ing-guillermo-quintero/Infra-Logistica/CADs/CAD_INFRA_LOG.jpeg

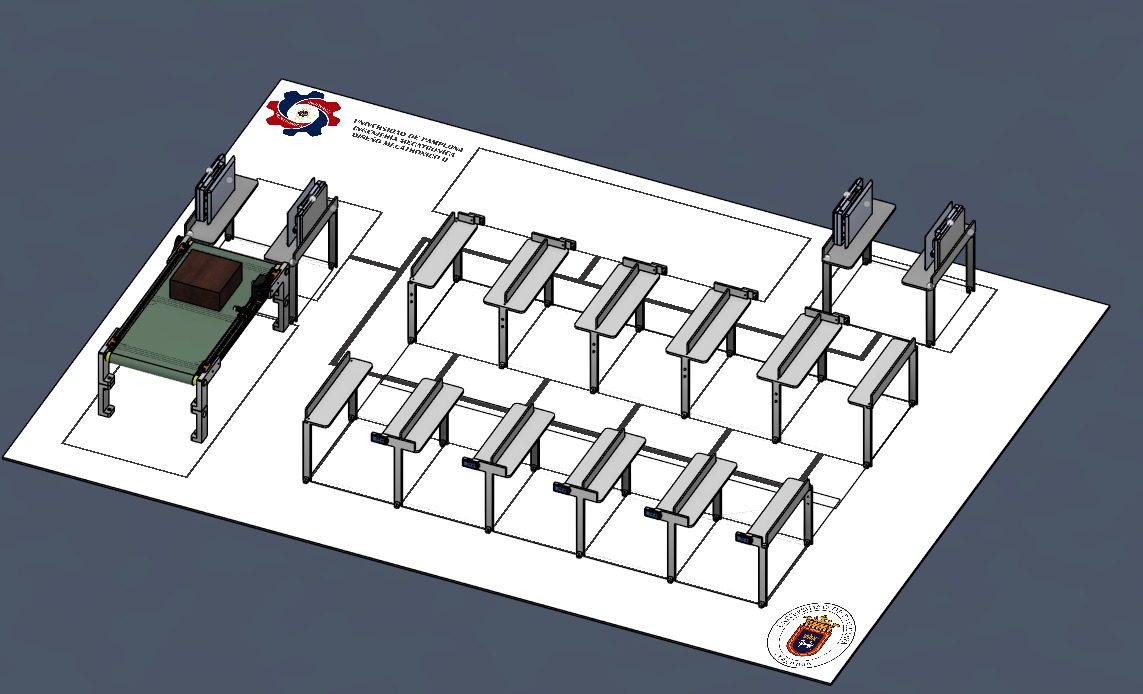
CADs/CAD_INFRA_LOG.jpeg
