ing-guillermo-quintero/Infra-Logistica/Sistema_Lectura_QR/Lector_QR_V2/codigos_qr/QR_messi.png

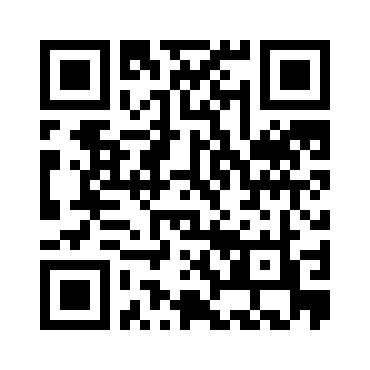
Sistema_Lectura_QR/Lector_QR_V2/codigos_qr/QR_messi.png
