ing-guillermo-quintero/Infra-Logistica/Sistema_Lectura_QR/Lector_QR_V2/imagenes/rosas.webp

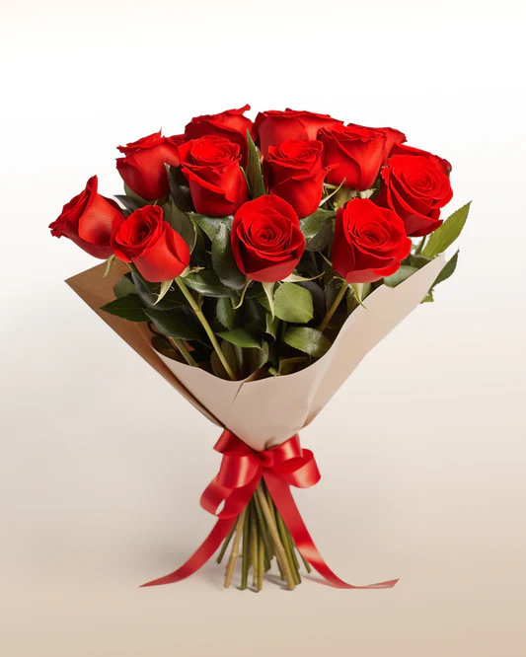
Sistema_Lectura_QR/Lector_QR_V2/imagenes/rosas.webp
